JuliansCastro/Sistema-proteccion-incendios/imgs/blink_8Mhz.png

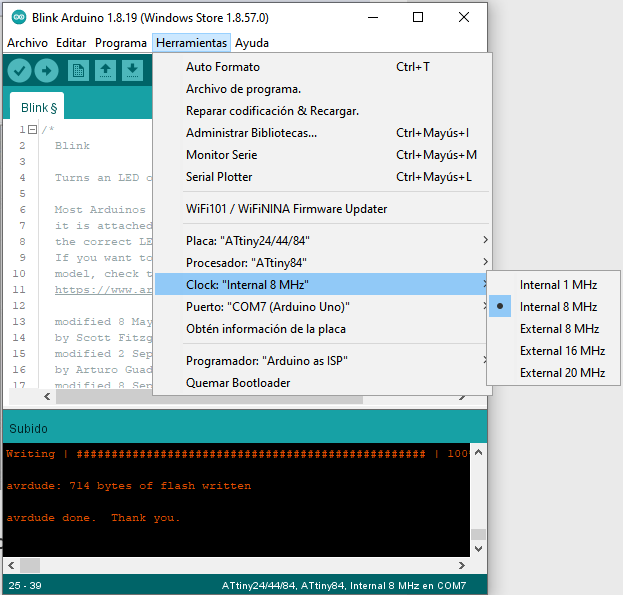
imgs/blink_8Mhz.png
