JuliansCastro/Sistema-proteccion-incendios/imgs/Gestor_Tarjetas_Attyny_David.png

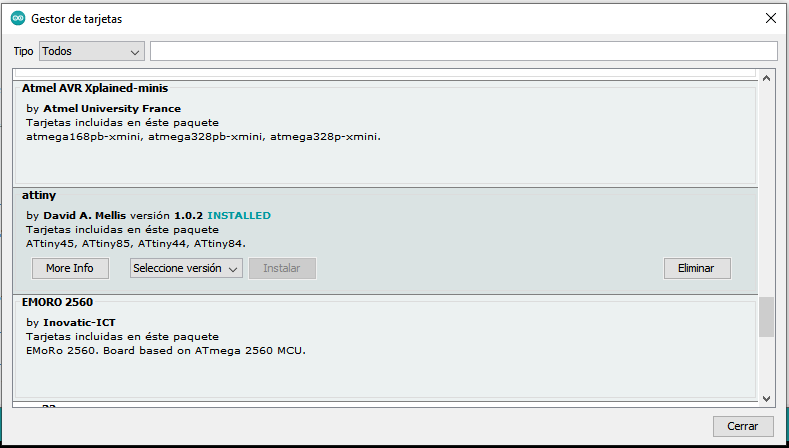
imgs/Gestor_Tarjetas_Attyny_David.png
