JuliansCastro/Sistema-proteccion-incendios/imgs/MonitorSerieAttiny84.png

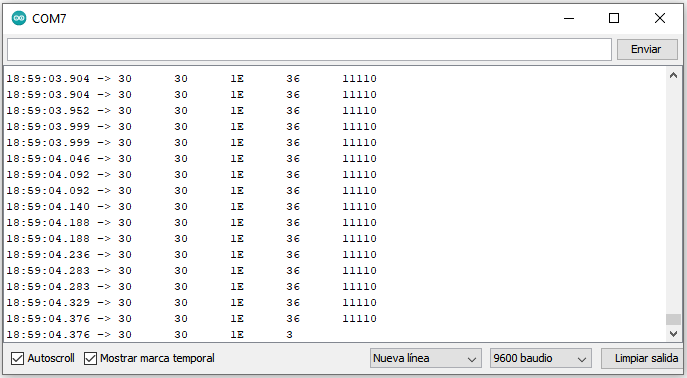
imgs/MonitorSerieAttiny84.png
