JuliansCastro/Sistema-proteccion-incendios/imgs/raspberry-pi-pico-w.jpg

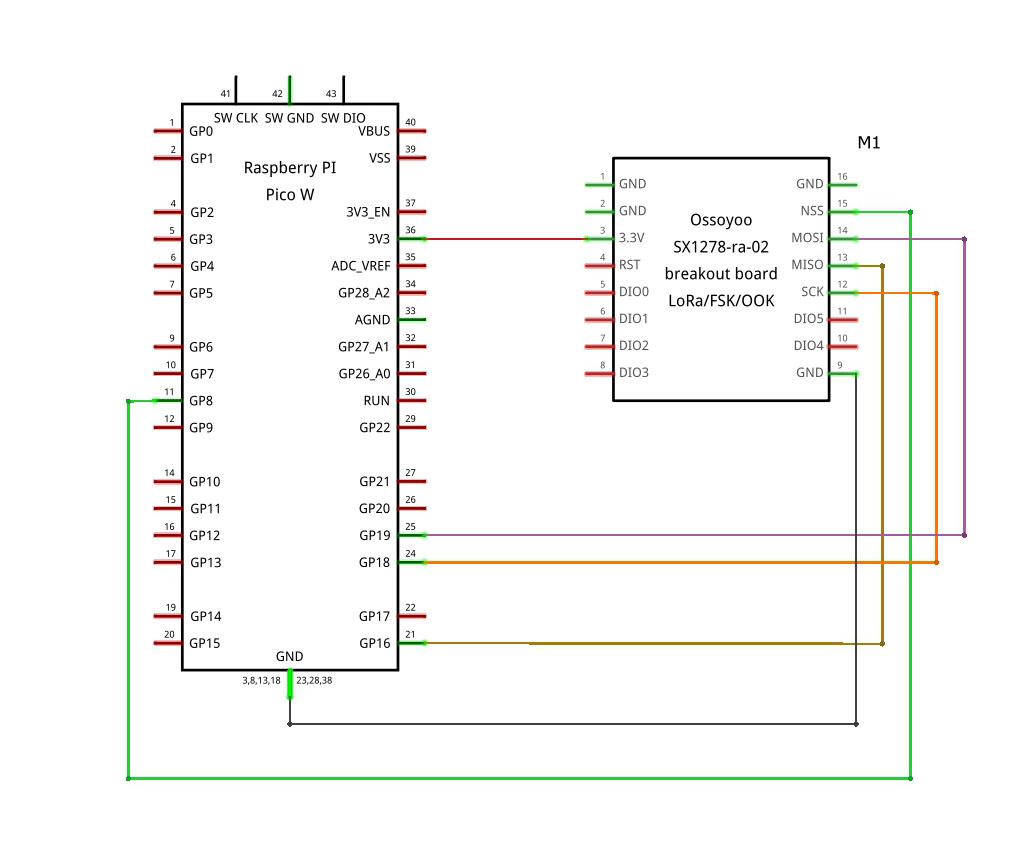
imgs/raspberry-pi-pico-w.jpg
